bigjosh/TSL/hardware/orientation photos/orientation S1.png

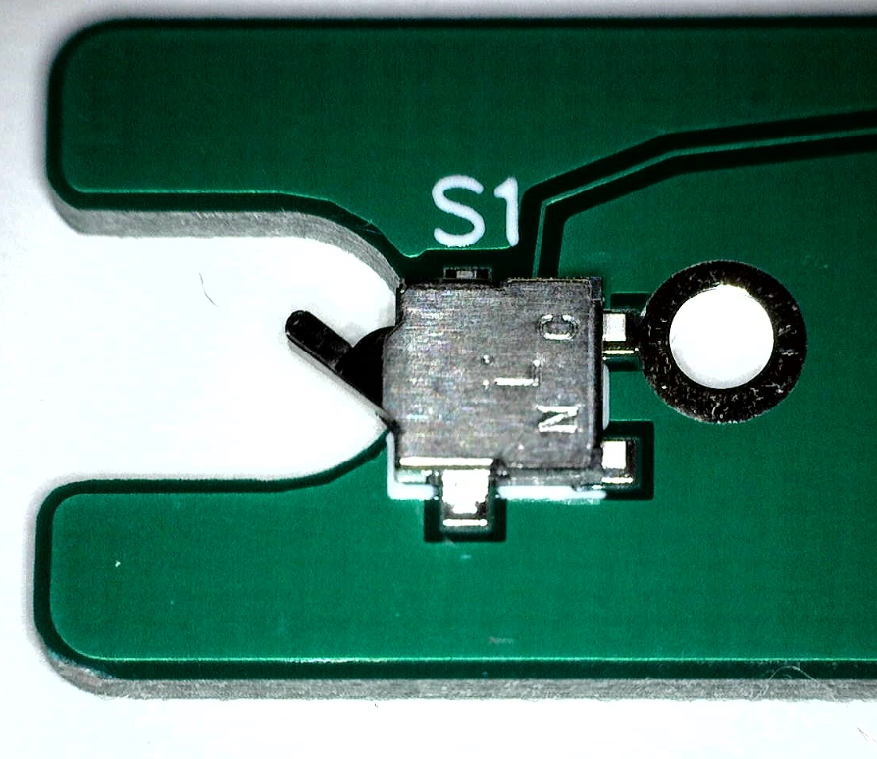
hardware/orientation photos/orientation S1.png
